ericrowe/Small-Parts-Bins/docs/plans/complete/2026-09-02-M02_qr_code_linking_and_bin_compartment_management_walkthrough.md

# Walkthrough: Plan M02 - Cross-Subsystem URL Linkages & Dynamic 1/2/3-Compartment Bin Management

## Completed Work & Changes Made

1. **Relational 1/2/3-Compartment SQLite Schema (`server/app/models.py`)**:
   - Updated `BinRecord` to model physical small-parts cassettes (`single`, `divided_2`, `divided_3`) with `compartment_count` (1, 2, or 3).
   - Added `BinCompartmentRecord` linking each bin slot index (1..3) to nullable `part_id`, `quantity_on_hand`, and `reorder_threshold`.
   - Updated `PartRecord` with relationship to `BinCompartmentRecord`.

2. **Self-Healing Schema Migrations & Numbered Bins Seeding (`server/app/database.py` & `seed.py`)**:
   - Implemented automatic SQLite schema migration handling table upgrades without manual intervention.
   - Seeded 24 physical numbered bins (`BIN-001` through `BIN-024`) across Lower and Upper carrier trays with baseline part assignments.

3. **Dynamic Bin & Part Web Views (`server/templates/` & `server/app/routes/`)**:
   - `part_detail.html` (`/p/{part_id}`): Mobile-friendly fastener technical spec view with thread pitch, tap drill, clearance drill, wrench size, and list of containing bins.
   - `bin_detail.html` (`/b/{bin_id}`): Visual 1, 2, or 3-compartment cassette viewer with dynamic "Assign Fastener Part" dropdowns and one-tap quantity counters.
   - `parts.html` (`/parts`): Bi-directional clickable column sorting and direct links to `/p/{part_id}` and `/b/{bin_id}`.
   - `dashboard.html` (`/`): Updated recent bins table displaying compartment counts and part pills.

4. **REST API Endpoints (`server/app/routes/api.py`)**:
   - `POST /api/bins/{bin_id}/compartments`: Dynamically assign/swap fastener parts in any compartment slot.
   - `PATCH /api/compartments/{comp_id}/quantity`: Adjust stock quantity for an individual compartment.
   - `GET /api/parts/{part_id}`: Retrieve technical specs with containing bins list.

5. **Hermetic Test Suite (`server/tests/`)**:
   - Created `tests/test_compartments_and_routes.py` covering 1/2/3-compartment bins, dynamic reassignments, and template rendering.
   - 12/12 server tests passing in 0.62s.
   - 10/10 workspace security and link tests passing.

## Validation Results

- **Unit & API Tests**: 12/12 tests passed (100% pass rate).
- **Security & Link Audit**: 10/10 tests passed with zero broken links.
- **Git State**: Clean commit and push to GitHub.
