ericrowe/Small-Parts-Bins/docs/plans/complete/2026-09-02-S01_fastapi_web_catalog_server_and_sqlite_database_walkthrough.md

# Walkthrough: Plan S01 - FastAPI Web Catalog Server, SQLite Parts Database & Automated Backup Pipeline

## Completed Work & Changes Made

1. **FastAPI Application & Concurrency Architecture (`server/app/`)**:
   - Built async SQLite database engine with Write-Ahead Logging (WAL) concurrency (`server/app/database.py`).
   - Defined relational models for `CategoryRecord`, `PartRecord`, `StorageLocationRecord`, `CarrierRecord`, and `BinRecord` (`server/app/models.py`).
   - Implemented automated database seed ingester on boot that translates `hardware/labels/data/fasteners.json` into structured relational parts with tap drill specifications and drive sizes (`server/app/seed.py`).
   - Built REST API endpoints (`server/app/routes/api.py`) and Jinja2 server-rendered views (`server/app/routes/views.py`).

2. **Responsive Workshop UI Templates (`server/templates/`)**:
   - `base.html`: Modern dark-mode Tailwind CSS layout with responsive navigation.
   - `dashboard.html`: Inventory overview with metric stat cards, category cards, and sample bins.
   - `parts.html`: Full-text searchable fastener catalog with bi-directional clickable column sorting across all fields.
   - `bin_detail.html`: Mobile-optimized QR scan landing page with one-tap stock decrement/increment adjusters (`+1`, `-1`, `+10`, `-10`).

3. **Master Rack Backup & Turnkey Disaster Recovery (`server/scripts/` & `server/docs/`)**:
   - Built `server/scripts/backup_parts.sh` capturing zero-downtime atomic snapshots via SQLite `VACUUM INTO`, running `PRAGMA integrity_check`, and pushing encrypted restic snapshots to Node 04 (`pi-backup.local:/srv/backups/restic/parts-database/`) with 14D / 8W / 12M retention.
   - Built `server/scripts/bootstrap_node.sh` for turnkey bare-metal provisioning and automated restoration.
   - Authored `server/docs/BACKUP_AND_RECOVERY.md` disaster recovery runbook.
   - Updated `rack/06_backup_strategy_master.md` with Parts-Database Node 04 landing zone.

4. **Hermetic Test Suite (`server/tests/`)**:
   - Authored `server/tests/test_server_api.py` and `server/tests/test_backup_pipeline.py`.
   - Verified 8/8 tests passing in 1.08s (100% pass rate).
   - Verified 10/10 documentation link and security auditor checks passing across workspace.

## Validation Results

- **Unit & API Tests**: 8/8 tests passed.
- **Security & Link Audit**: 10/10 tests passed with 0 broken links.
- **Git State**: Clean commit and push to GitHub.
