ericrowe/Small-Parts-Bins/docs/plans/complete/2026-09-02-M01_repository_categorization_and_server_staging_plan.md

# Plan M01: Repository Categorization, Subsystem Restructuring & Web Catalog Server Staging

## 1. Goal Description

The `Parts-Database` repository currently houses both mechanical 3D print assets (carriers, cassettes, labels, render scripts) at the root level and is preparing to introduce a modern Web Catalog Server & QR Scanner microservice.

This master plan executes a clean, structured repository reorganization and establishes the multi-prefix plan lifecycle:
1. Group all physical 3D fabrication models, parametric generators, and label artwork into a dedicated **`hardware/`** directory (`hardware/carriers/`, `hardware/cassettes/`, `hardware/labels/`, `hardware/scripts/`, `hardware/plans/`).
2. Scaffold the dedicated **`server/`** directory (`server/app/`, `server/database/`, `server/static/`, `server/templates/`, `server/tests/`) for the upcoming web catalog server.
3. Establish the centralized **Multi-Prefix Planning System** in `docs/plans/`:
   - `MNN_<name>_plan.md`: Master cross-subsystem epics (e.g. End-to-end QR code generation $\leftrightarrow$ scanning $\leftrightarrow$ database resolution).
   - `HNN_<name>_plan.md`: Hardware subsystem plans (CAD models, carrier trays, label cut sheets).
   - `SNN_<name>_plan.md`: Server subsystem plans (FastAPI routes, SQLite models, HTML5 camera QR scanner UI).
4. Update all documentation, generator scripts, and internal relative links to preserve 100% link portability and build integrity.

---

## 2. Architecture & Directory Hierarchy Diagram

```mermaid
flowchart TD
    subgraph Root["Parts-Database Repository Root"]
        AGENTS["AGENTS.md (Master Directives)"]
        README["README.md (Architecture & Overview)"]
        
        subgraph Hardware["hardware/ (Physical Fabrication & CAD)"]
            Carriers["carriers/ (Gridfinity Trays & Inserts)"]
            Cassettes["cassettes/ (Slide Bins & Dividers)"]
            Labels["labels/ (Artwork, Fasteners DB & SVG Renderers)"]
            HScripts["scripts/ (Render & Build Automation)"]
            HPlans["plans/ (Hardware Design Archives)"]
        end
        
        subgraph Server["server/ (Web Catalog & QR Microservice)"]
            App["app/ (FastAPI / Routing / QR API)"]
            DB["database/ (SQLite Schema & Models)"]
            UI["templates/ & static/ (Responsive UI & QR Scanner)"]
            Tests["tests/ (Hermetic Test Suite)"]
        end
        
        subgraph Docs["docs/plans/ (Centralized Multi-Prefix Planning Hub)"]
            P_Reg["AGENTS.md (Master Registry)"]
            P_M["MNN_* (Master Cross-Subsystem Plans)"]
            P_H["HNN_* (Hardware Subsystem Plans)"]
            P_S["SNN_* (Server Subsystem Plans)"]
            P_Comp["complete/ (Archived Plans & Walkthroughs)"]
            P_Ideas["IDEAS.md (Categorized Backlog)"]
        end
    end
```

---

## 3. Code & File Modifications

### Component 1: Hardware Category Migration
- **`[NEW / MOVE]`** `Carriers/` $
ightarrow$ `hardware/carriers/`
- **`[NEW / MOVE]`** `Cassettes/` $
ightarrow$ `hardware/cassettes/`
- **`[NEW / MOVE]`** `Labels/` $
ightarrow$ `hardware/labels/`
- **`[NEW / MOVE]`** `scripts/` $
ightarrow$ `hardware/scripts/`
- **`[NEW / MOVE]`** `Plans/` $
ightarrow$ `hardware/plans/`

### Component 2: Script & Generator Path Updates
- **`[MODIFY]`** `hardware/scripts/generate_all_renders.py`: Update paths referencing `Carriers/`, `Cassettes/`, and `Labels/` to `hardware/...`.
- **`[MODIFY]`** `hardware/labels/generate_labels.py`: Update default output directory to `hardware/labels/build`.

### Component 3: Server Directory Scaffolding
- **`[NEW]`** `server/`: Scaffold `app/`, `database/`, `static/`, `templates/`, and `tests/` directories with `.gitkeep` markers.

### Component 4: Planning Framework & Documentation Synchronization
- **`[MODIFY]`** [`docs/plans/AGENTS.md`](./AGENTS.md): Codify the multi-prefix planning standard (`MNN_`, `HNN_`, `SNN_`).
- **`[MODIFY]`** [`docs/plans/IDEAS.md`](./IDEAS.md): Structure categorized backlog sections.
- **`[MODIFY]`** [`README.md`](../README.md): Update directory structure reference table and component links.
- **`[MODIFY]`** [`AGENTS.md`](../AGENTS.md): Update hardware CAD generation rules and path invariants.

---

## 4. Test Updates & Specifications

1. **Link & Security Audits**:
   - Run `tests/test_documentation_links.py` and `tests/test_security_auditor.py` across workspace to ensure zero broken links.
2. **Hardware Generator Verification**:
   - Verify `python3 hardware/labels/generate_labels.py` runs and locates `hardware/labels/data/fasteners.json`.

---

## 5. Documentation Updates

- **`[MODIFY]`** [`README.md`](../README.md): Document `hardware/`, `server/`, and `docs/plans/` architecture.
- **`[MODIFY]`** [`AGENTS.md`](../AGENTS.md): Update path invariants.

---

## 6. Verification Plan

### Automated Verification
```bash
# 1. Run workspace relative link and security tests
.venv/bin/python -m pytest tests/test_documentation_links.py tests/test_security_auditor.py -q

# 2. Verify label generation script locates data files
python3 hardware/labels/generate_labels.py --help
```

### Manual Verification
1. Inspect directory structure via `ls -la` and `tree -L 2`.
2. Confirm clean separation between `hardware/`, `server/`, and `docs/plans/`.
