ericrowe/Small-Parts-Bins/docs/images/rocker_insert_dual_slot_multiview.png

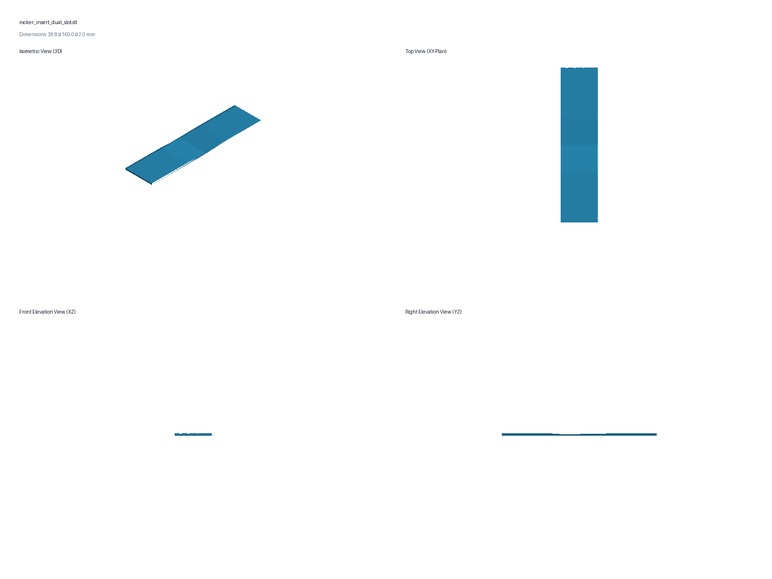
docs/images/rocker_insert_dual_slot_multiview.png
