ericrowe/Small-Parts-Bins/hardware/cassettes/glass_slide_cassette_40x80/build/cassette_body_v0_8.stl

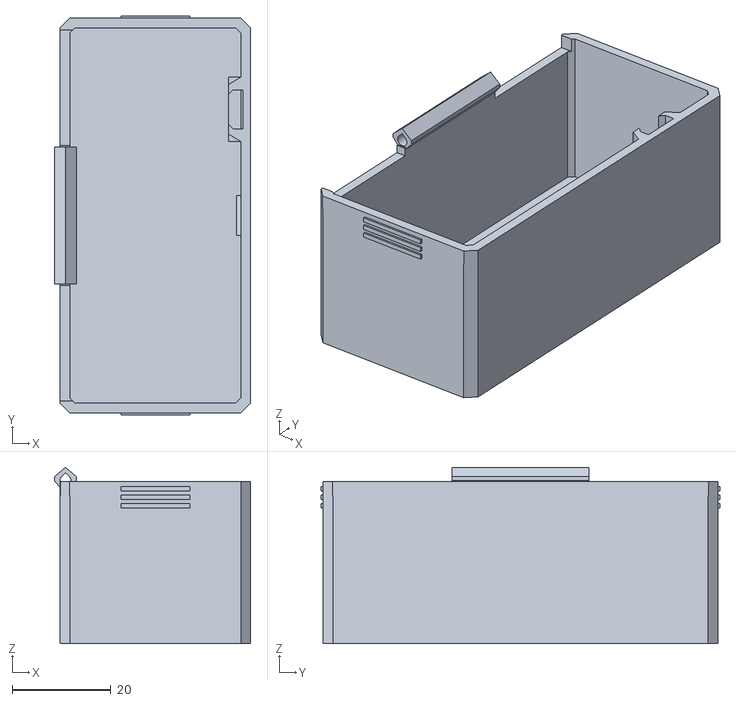
[picture p27: CAD file, 2026-08-29]
hardware/cassettes/glass_slide_cassette_40x80/build/cassette_body_v0_8.stl
39.8 x 80.8 x 35.7
