ericrowe/Small-Parts-Bins/hardware/cassettes/glass_slide_cassette_40x80/build/divider_card_1_2mm.stl

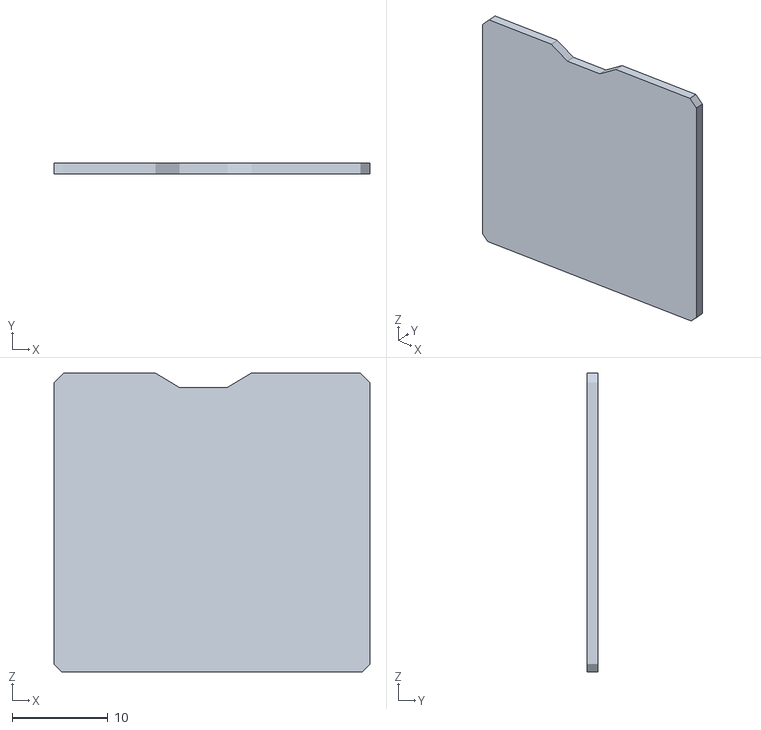
[picture p30: CAD file, 2026-08-28]
hardware/cassettes/glass_slide_cassette_40x80/build/divider_card_1_2mm.stl
33.0 x 1.20 x 31.2
