ericrowe/Small-Parts-Bins/hardware/cassettes/glass_slide_cassette_40x80/build/cassette_body_v0_8_multiview.png

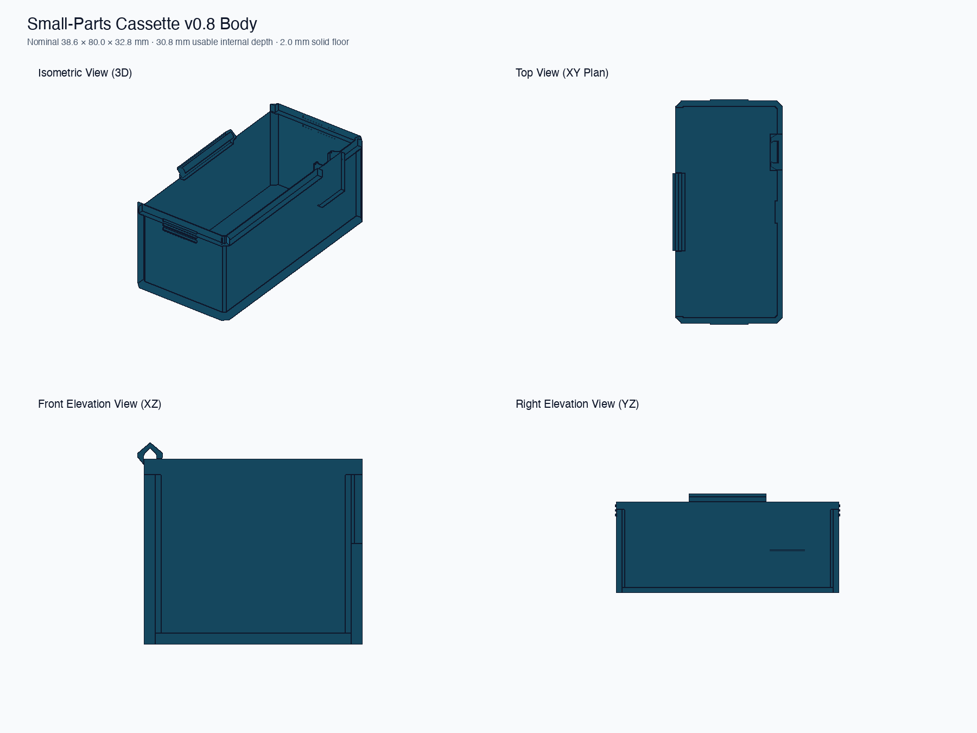
hardware/cassettes/glass_slide_cassette_40x80/build/cassette_body_v0_8_multiview.png
