ericrowe/Small-Parts-Bins/hardware/labels/build/brass_heat_set_insert_assortment_preview_strip.png

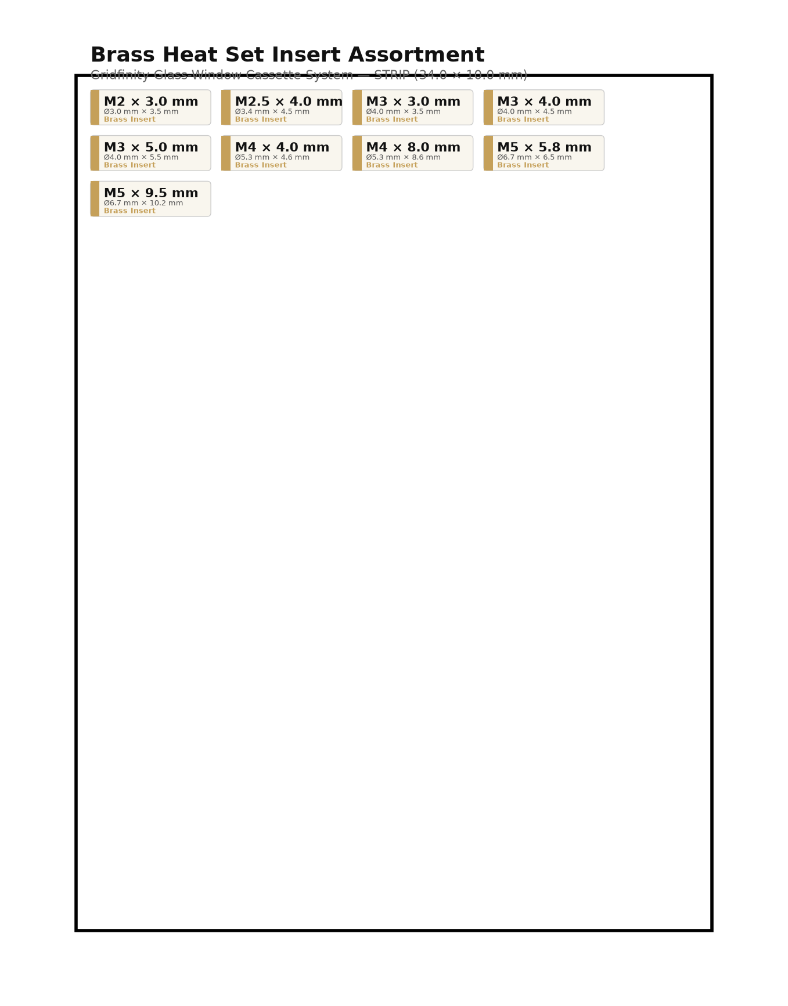
hardware/labels/build/brass_heat_set_insert_assortment_preview_strip.png
