ericrowe/Small-Parts-Bins/hardware/labels/build/imperial_sae_socket_assortment_preview_strip.png

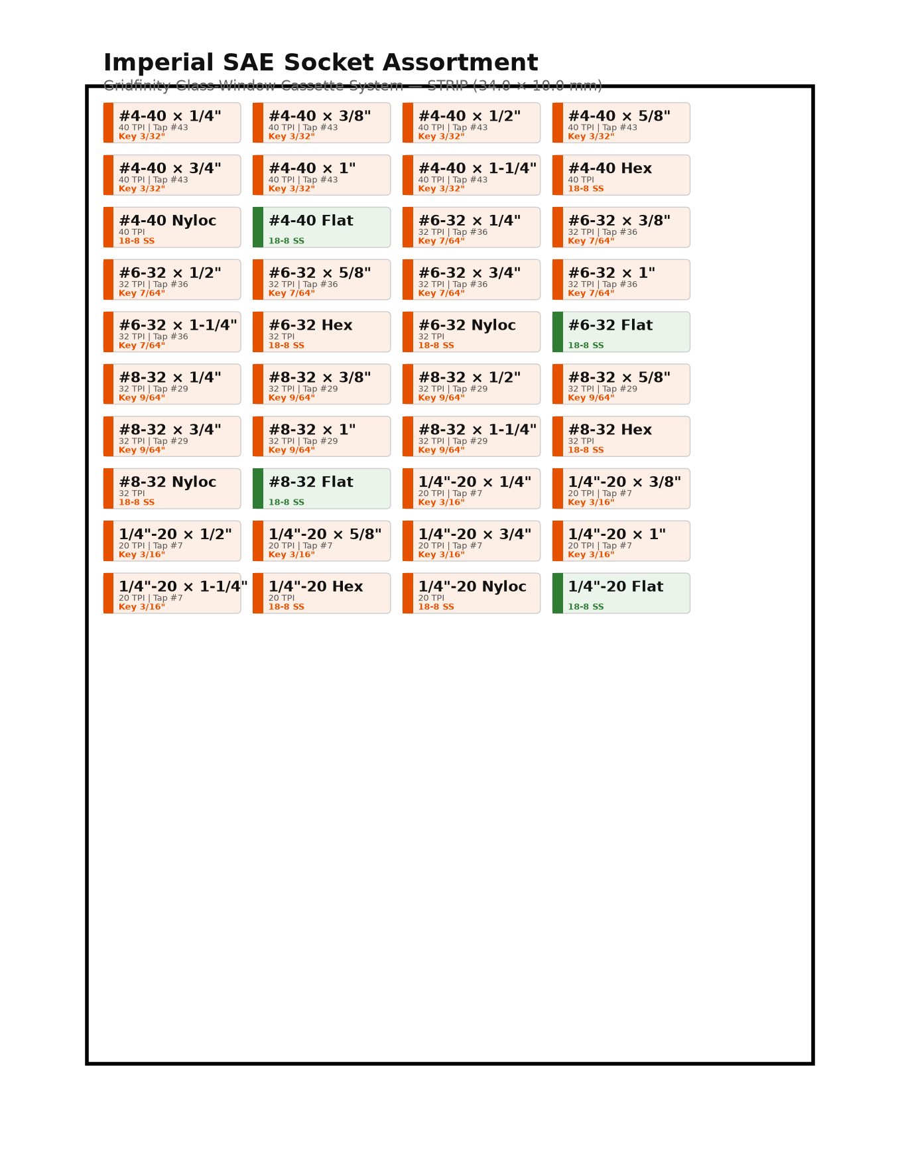
hardware/labels/build/imperial_sae_socket_assortment_preview_strip.png
