ericrowe/Small-Parts-Bins/hardware/labels/build/metric_m4_m5_m6_structural_assortment_preview_strip.png

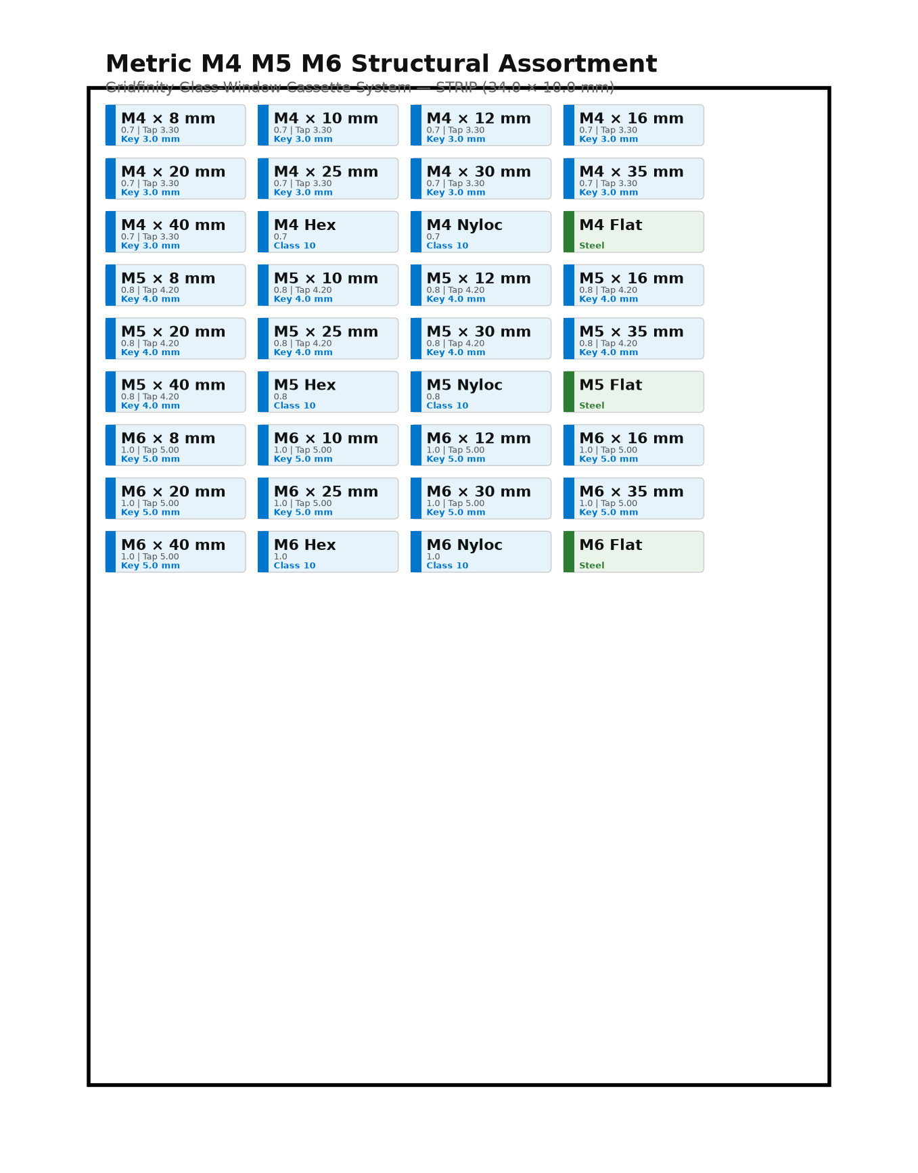
hardware/labels/build/metric_m4_m5_m6_structural_assortment_preview_strip.png
