ericrowe/Small-Parts-Bins/hardware/plans/Completed/2026-08-28-001-validate-14u-carrier-stack-walkthrough.md

# Plan 001 Walkthrough — Validate the 14U Carrier Stack

- Plan: `Plans/Completed/2026-08-28-001-validate-14u-carrier-stack.md`
- Completed: 2026-08-28
- Outcome: **Physically Verified and Accepted**

## 1. Executive Summary

Plan 001 evaluated the two-carrier vertical stack architecture within the measured drawer height constraint (**111.125 mm / 4 3/8 in**). Two identical 3 × 4 × 7U carrier trays (`build/carrier_3x4_7u_v0_1.stl`) were fabricated in PETG, loaded into the target drawer on top of existing Gridfinity baseplates, and tested for stacking engagement, stability, and vertical clearance.

The physical test confirmed:
1. Two 7U carriers engage securely in a 14U stack (.40	ext{ mm}$ overall height including the exposed stacking lip).
2. The stacked assembly fits smoothly into the target drawer with plenty of clearance below the .125	ext{ mm}$ ceiling.
3. Carrier v0.1 successfully interfaces with standard Gridfinity baseplates.
4. Carrier v0.1 is accepted as the canonical 3 × 4 carrier baseline for the system.

## 2. Dimensional & Vertical Tolerance Budget

| Feature / Datum | Modeled Value | Physical Test Finding |
|---|---:|---|
| Carrier Outside Footprint | .5 	imes 167.5	ext{ mm}$ | Fits 3 × 4 Gridfinity envelope |
| Internal Throat (narrowest lip) | .3 	imes 162.3	ext{ mm}$ | Clears six 40 × 80 cassette envelopes |
| Single Carrier Total Height | .40	ext{ mm}$ | Measured and verified |
| Single Carrier Engaged Height | .00	ext{ mm}$ (7U) | Standard Gridfinity 7U pitch |
| Two-Carrier Stack Height | .40	ext{ mm}$ (14U) | Verified |
| Measured Drawer Ceiling | .125	ext{ mm}$ | Ample clearance observed during physical drawer test |
| Minimum Wall Thickness | .60	ext{ mm}$ (throat) / .00	ext{ mm}$ floor | Meets $>2.0	ext{ mm}$ structural rule |

## 3. Physical Fabrication and Test Results

- **Material & Slicing:** Both carrier trays were printed in PETG on a 0.4 mm nozzle, 0.20 mm layer height, 4 perimeters, support-free.
- **Baseplate Engagement:** The bottom .75	ext{ mm}$ stepped feet align with standard 42 mm Gridfinity baseplate sockets without binding.
- **Carrier Stacking:** The upper carrier's lower perimeter registers securely within the lower carrier's upper stacking lip.
- **Ergonomics:** Outer walls are solid continuous perimeters; extraction of cassettes is achieved via cassette top-edge grab features.

## 4. Key Architectural Findings for Subsequent Plans

- **Upper Tray Foot Protrusion (Input to Plan 002):** The upper carrier's  	imes 4$ array of Gridfinity feet hangs down .75	ext{ mm}$ below the  = 49.00	ext{ mm}$ engagement shelf into the lower tray cavity. The lowest point of the upper tray is at  = 44.25	ext{ mm}$. With the lower tray floor at  = 6.75	ext{ mm}$, total available vertical height for cassettes is .50	ext{ mm}$. This established the .00	ext{ mm}$ closed cassette height standard (.50	ext{ mm}$ clearance) in Plan 002.

## 5. Artifacts and Verification Records

- Printable Carrier Model: `Carriers/carrier_3x4_14u_test/build/carrier_3x4_7u_v0_1.stl` (2,900 triangles, 0 boundary edges, 0 non-manifold edges, 0 degenerate triangles).
- Carrier README: `Carriers/carrier_3x4_14u_test/README.md`
- Physical Test Notes: `Carriers/carrier_3x4_14u_test/PHYSICAL_TEST_NOTES.md`
