ericrowe/Small-Parts-Bins/hardware/cassettes/glass_slide_cassette_40x80/PHYSICAL_TEST_NOTES.md

# Cassette v0.7 full-lid integration — physical-test notes

## Print record

- Printer:
- PETG product:
- Nozzle / layer height / perimeters:
- Slicer and version:
- Other settings:
- Reused body revision/specimen:
- Pane width: 24.9 mm reported
- Pane length / thickness:
- Pane edge condition:

## As-printed lid inspection

- Pane channel clear without cleanup:
- Opposite ledges free of obstructive sag:
- Pane tongue returns fully:
- Tongue/root whitening, cracking, or permanent set:
- Hinge roots continuous:
- Lid bores clear:
- Other defects:

## Pane installation and capture

- Pane slides to far stop without force:
- Shoulder returns behind pane end:
- Relaxed tongue does not press on pane face:
- Positive pull retention passes:
- Pane rattle, bowing, or scratching:
- Escape path observed:
- Pane replacement cycles completed, up to 25:
- Final tongue return and root condition:

## Reused-body assembly

- Body revision:
- 1.75 mm filament pin installs by hand:
- Hinge sweep through at least 120 degrees:
- Body latch closes and releases normally:
- Fingernail relief remains usable:
- Glass/label remains clear of handling loads:

## Supported behavior and containment

- Full-perimeter stiffness compared with coupon:
- Loaded rollover protocol/result:
- Knockout comparison protocol/result:
- Carrier fit and stacking-plane clearance:
- Glass/frame damage:
- Final disposition:

Stop immediately for glass damage, unsafe ejection, hinge/root fracture,
permanent pane-latch deformation, incomplete latch return, or any need to force
or pry the glass. Use a protective enclosure for rollover or impact tests.
