ericrowe/Small-Parts-Bins/hardware/labels/build/test_preview.png

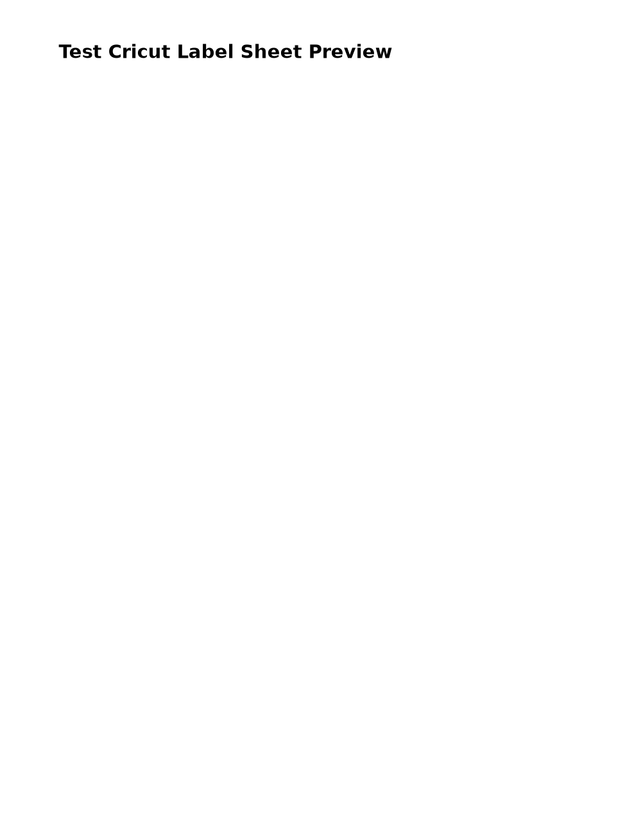
hardware/labels/build/test_preview.png
